F4INX/f4inx-diff-line-demo/pcb/diff-line-2-layers.png

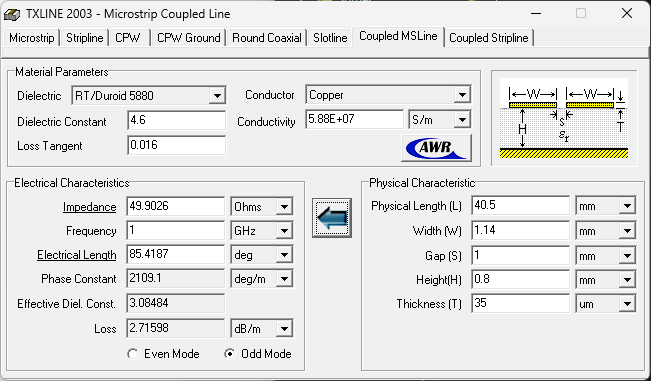
pcb/diff-line-2-layers.png
