F4INX/f4inx-diff-line-demo/pcb/diff-line-4-layers-alt1-even.png

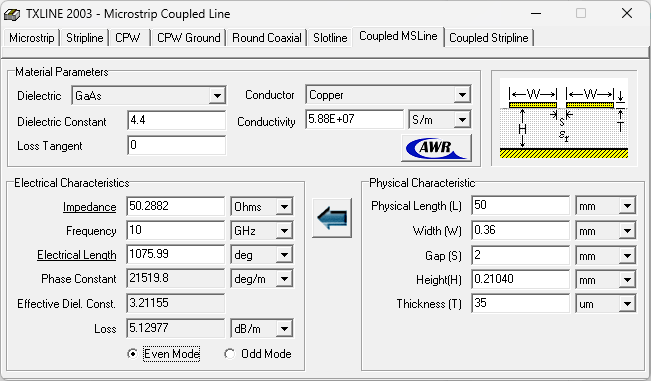
pcb/diff-line-4-layers-alt1-even.png
