F4INX/f4inx-diff-line-demo/pcb/se-line-2-layers.png

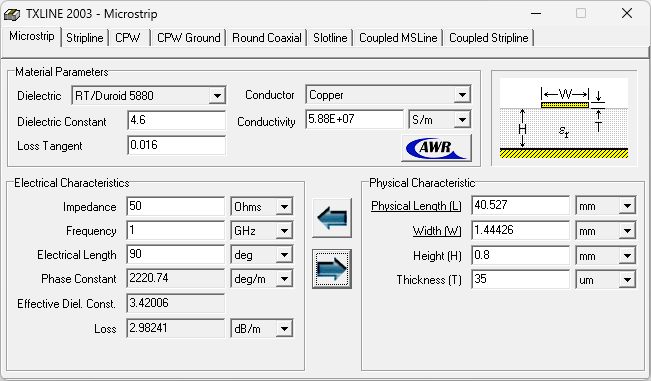
pcb/se-line-2-layers.png
