F4INX/f4inx-diff-line-demo/pictures/20260227_033025.jpg

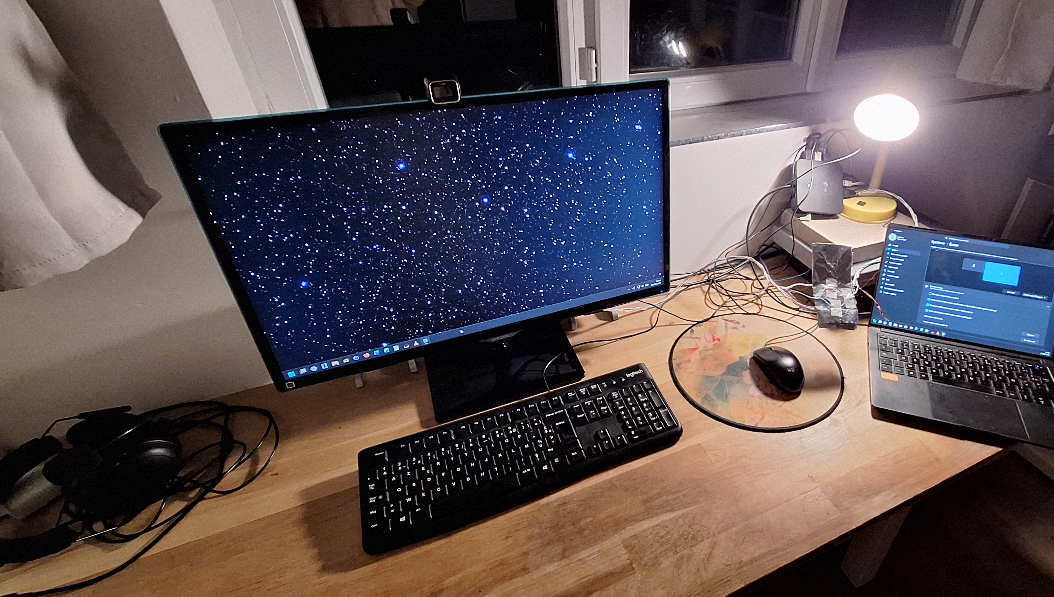
pictures/20260227_033025.jpg
