F4INX/f4inx-diff-line-demo/pictures/20260227_033705.jpg

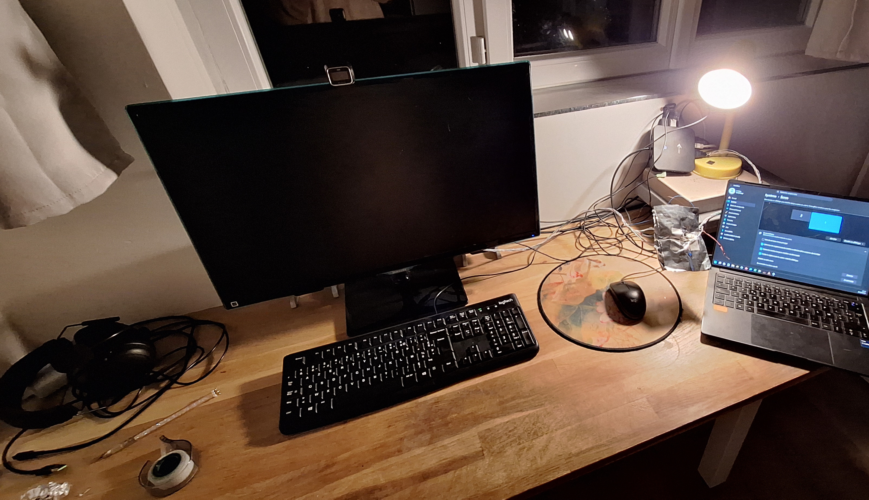
pictures/20260227_033705.jpg
