F4INX/f4inx-diff-line-demo/sim/sim-diff-pair-butterfly-eye.png

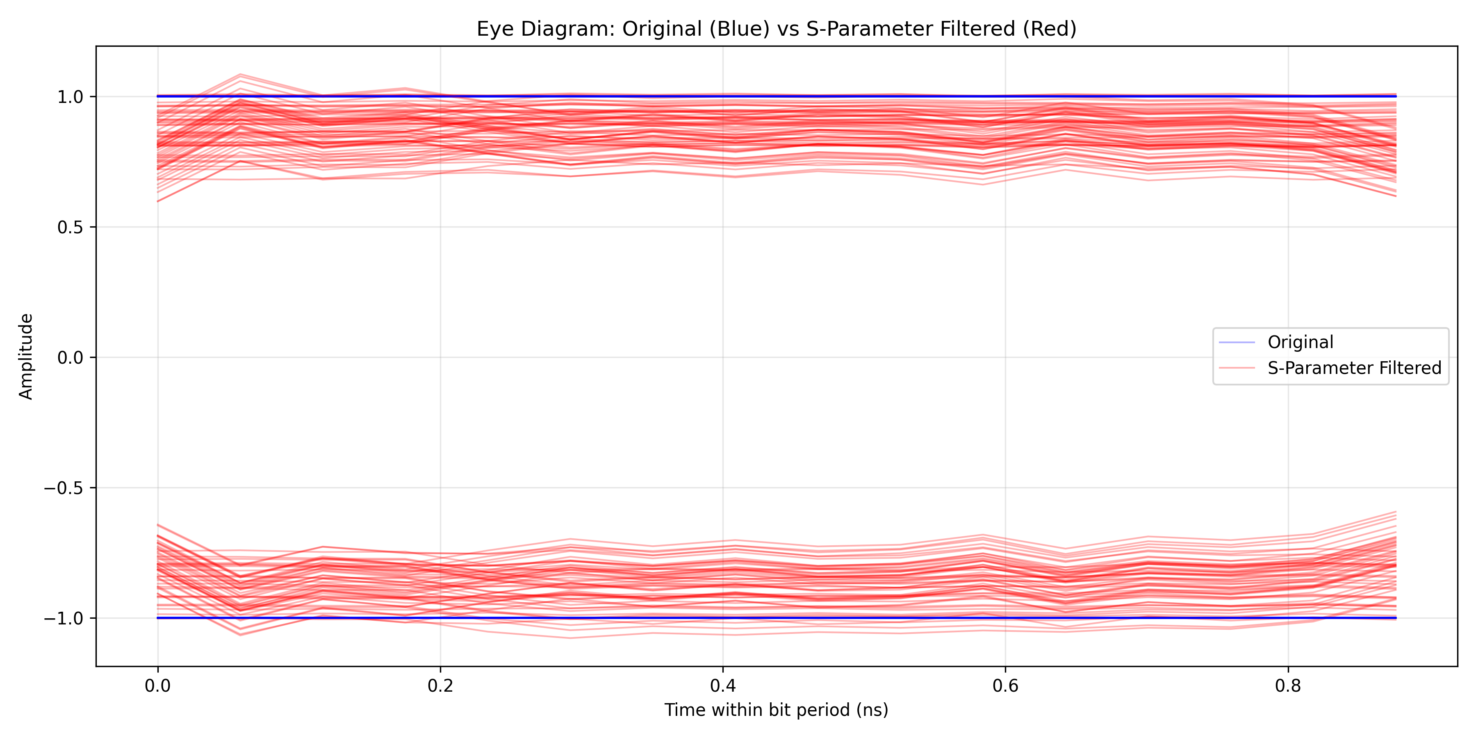
sim/sim-diff-pair-butterfly-eye.png
