F4INX/f4inx-diff-line-demo/sim/sim-diff-pair-cross-butterfly-field.png

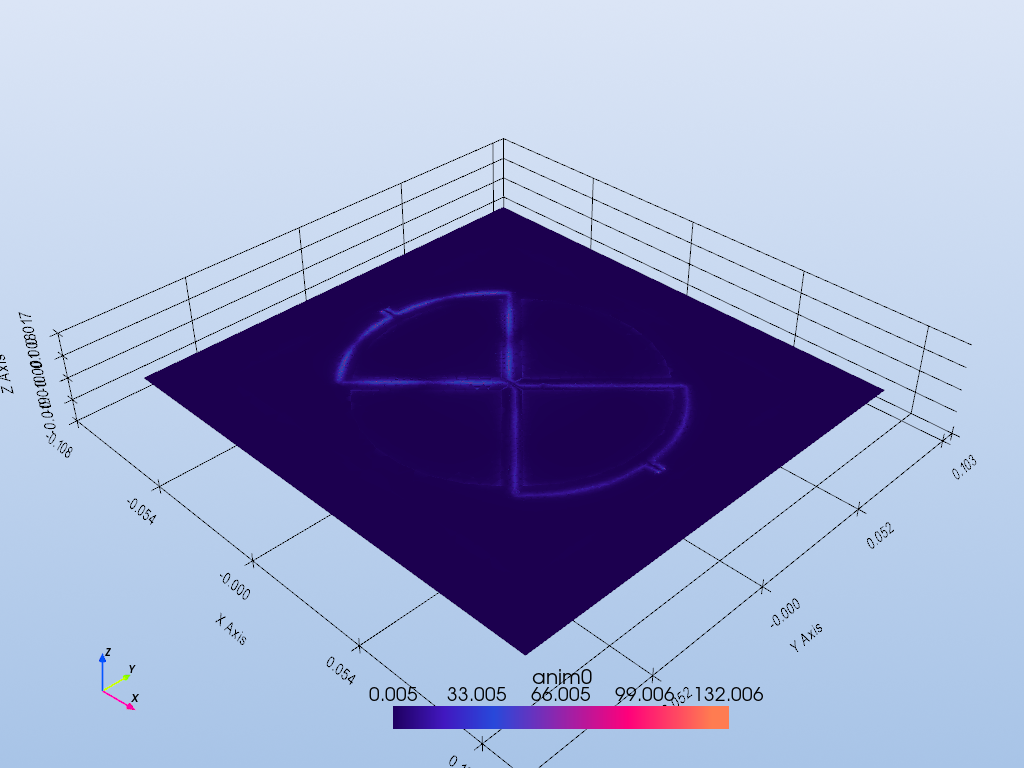
sim/sim-diff-pair-cross-butterfly-field.png
