F4INX/f4inx-diff-line-demo/sim/sim-diff-pair-cross-butterfly-freq.png

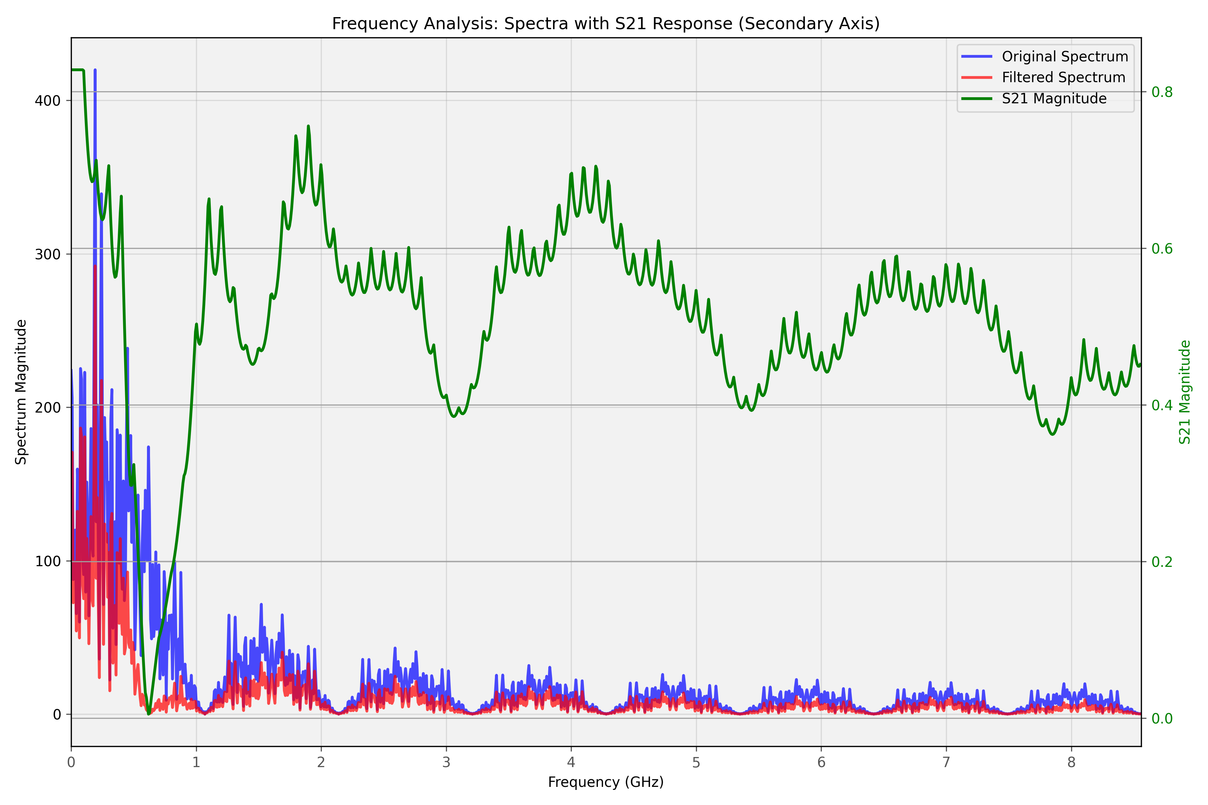
sim/sim-diff-pair-cross-butterfly-freq.png
