F4INX/f4inx-diff-line-demo/sim/sim-diff-pair-cross-butterfly-model-initial.png

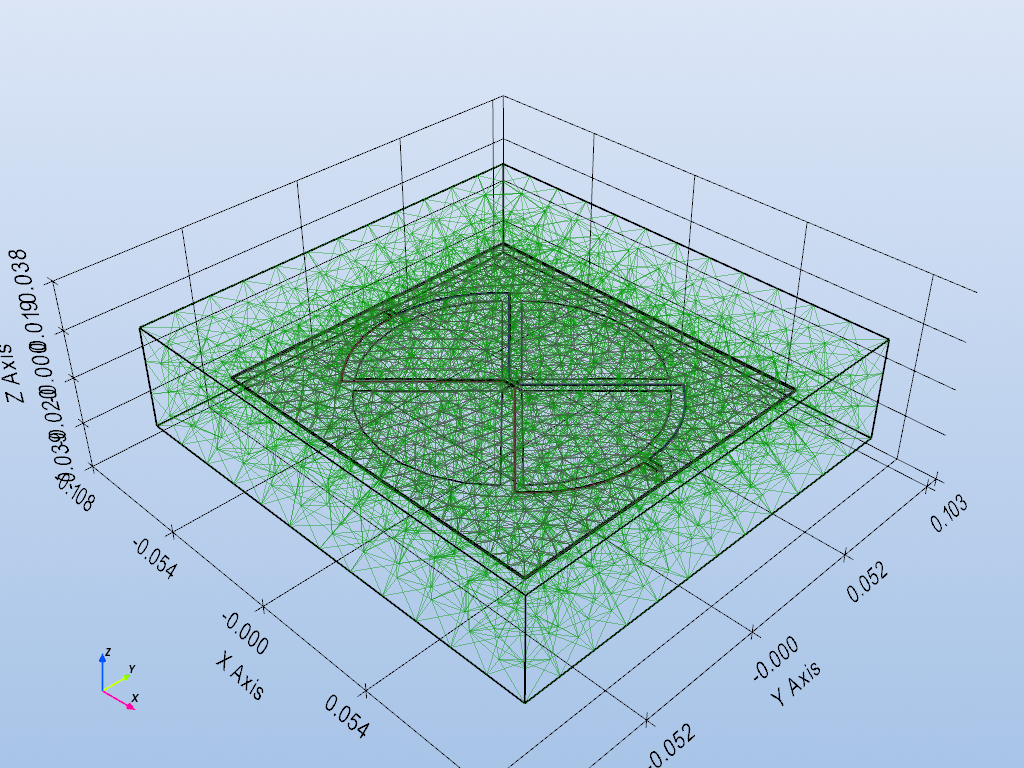
sim/sim-diff-pair-cross-butterfly-model-initial.png
