F4INX/f4inx-diff-line-demo/sim/sim-diff-pair-cross-butterfly-time-domain.png

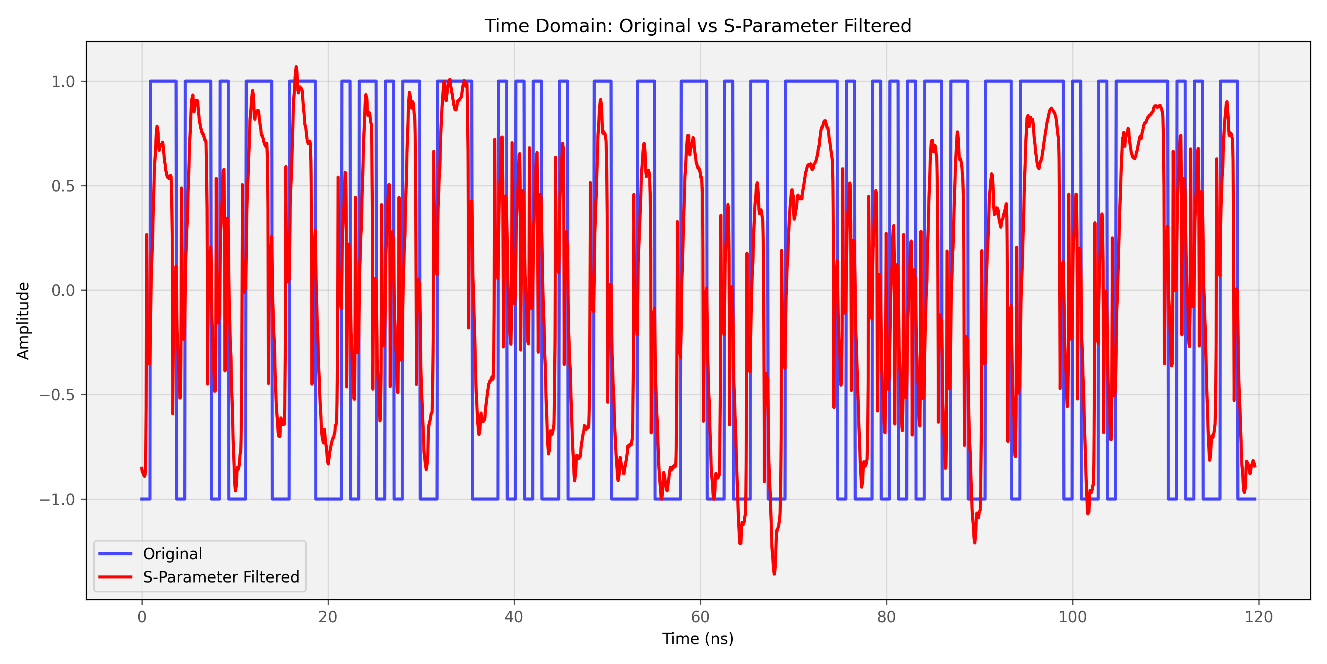
sim/sim-diff-pair-cross-butterfly-time-domain.png
