F4INX/f4inx-diff-line-demo/sim/sim-diff-pair-ref-butterfly-time-domain.png

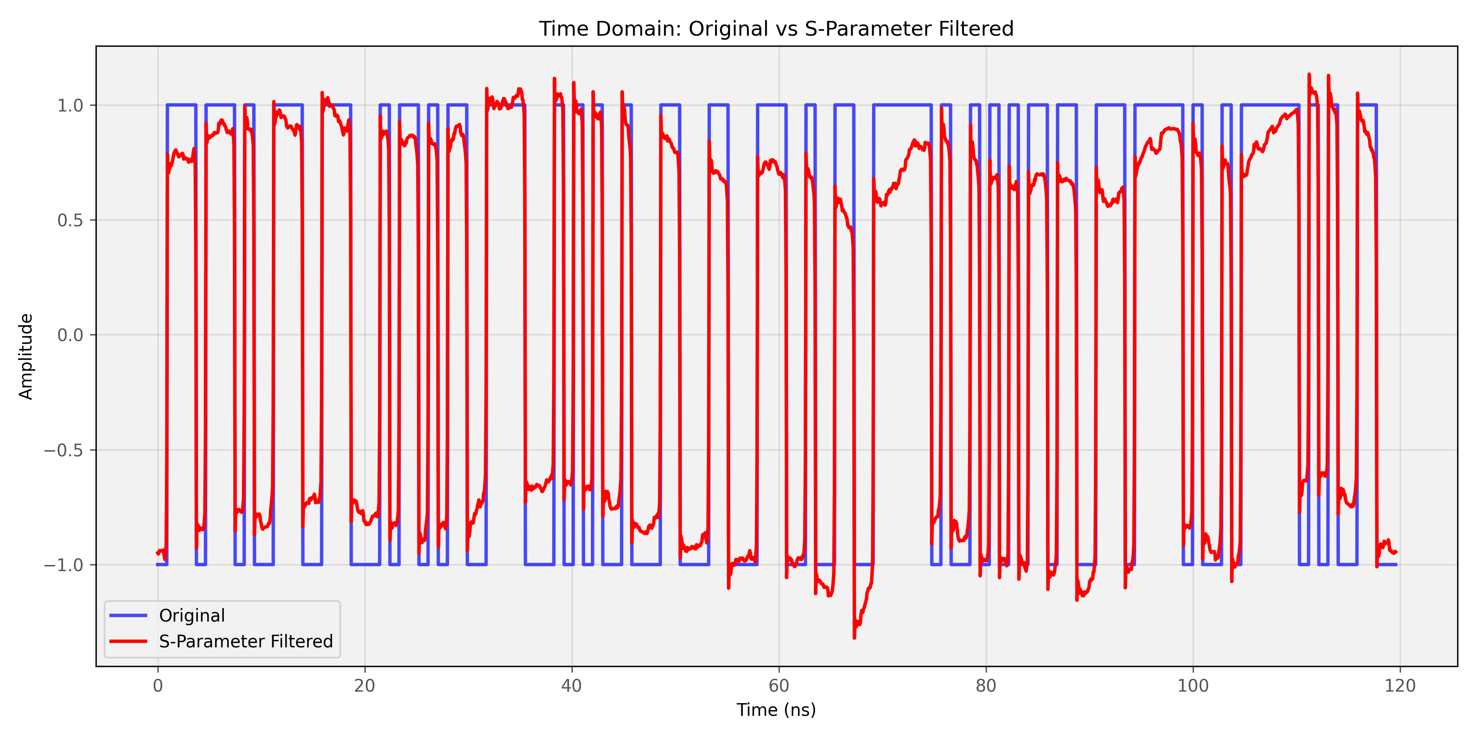
sim/sim-diff-pair-ref-butterfly-time-domain.png
