F4INX/f4inx-diff-line-demo/sim/sim-diff-pair-slot-butterfly-freq.png

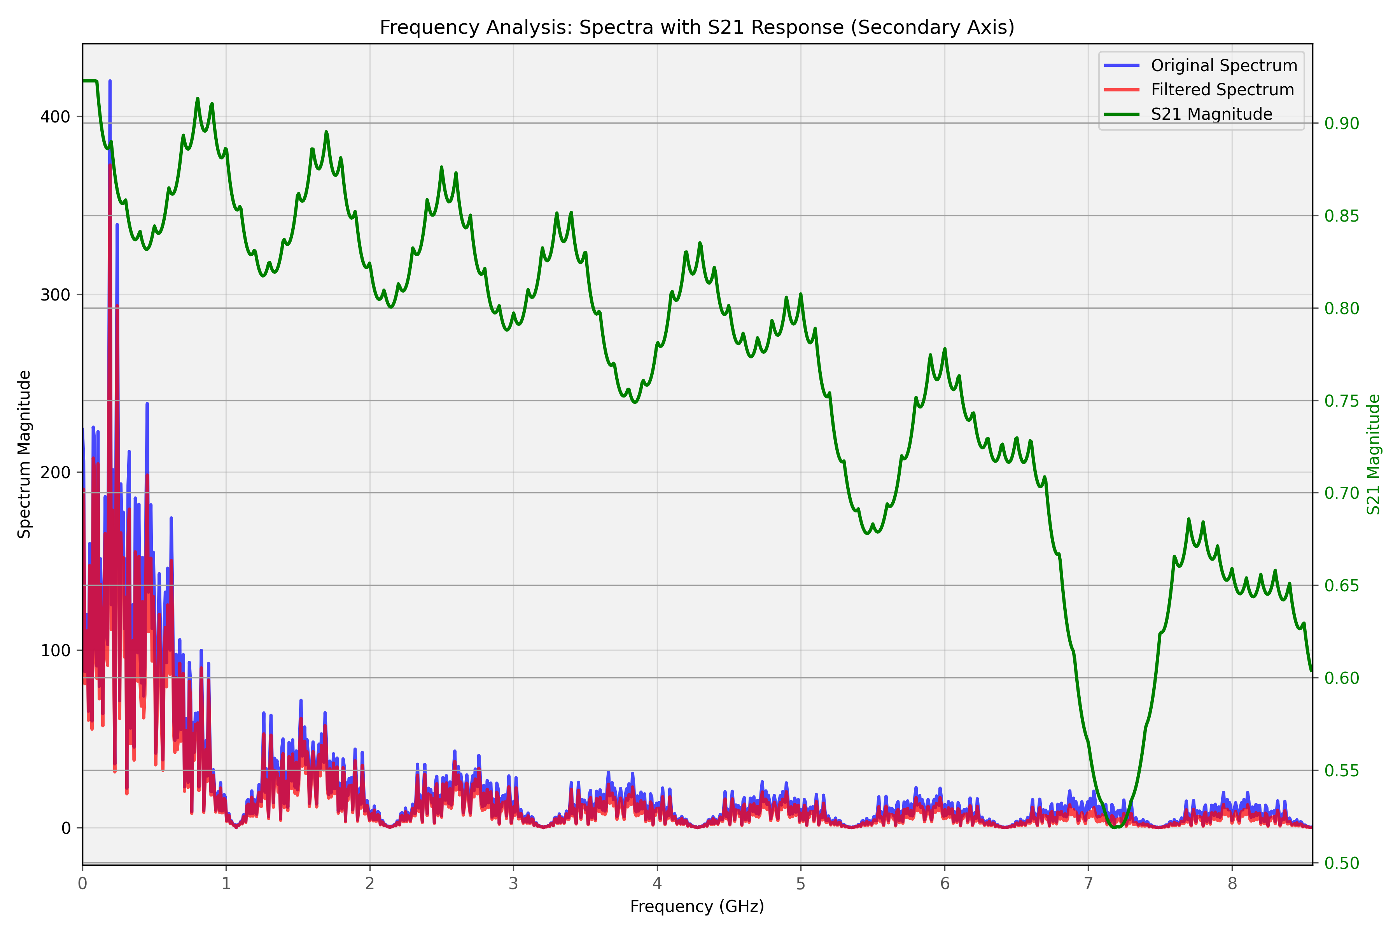
sim/sim-diff-pair-slot-butterfly-freq.png
