F4INX/f4inx-diff-line-demo/sim/sim-diff-pair-slot-butterfly-model-initial.png

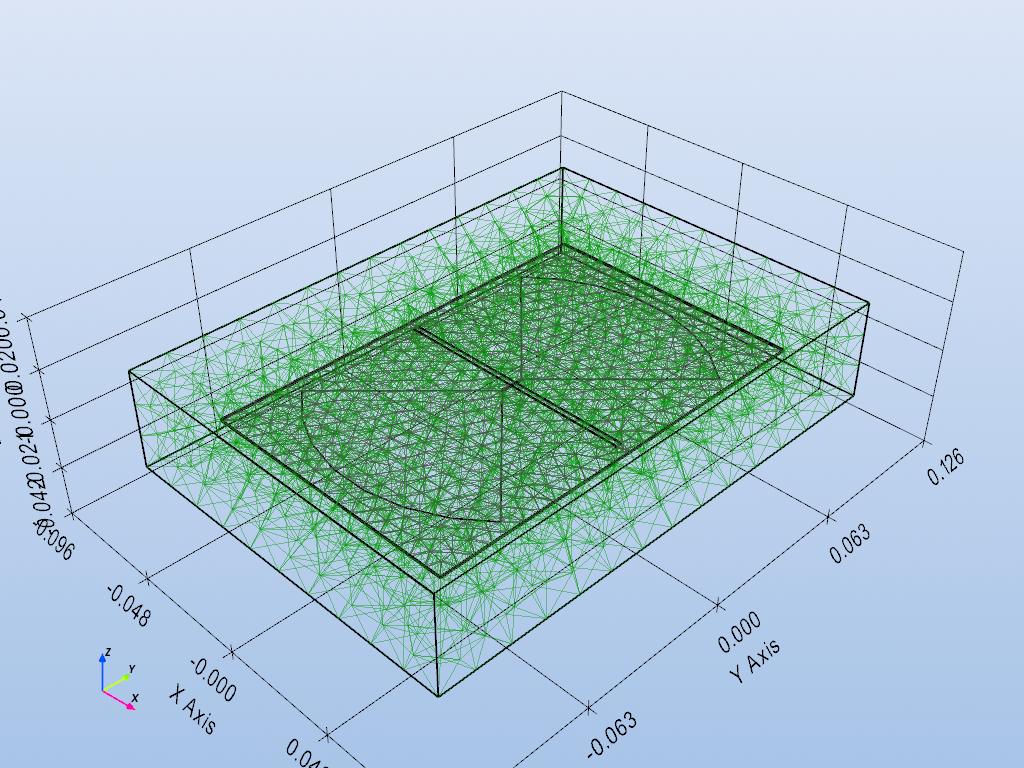
sim/sim-diff-pair-slot-butterfly-model-initial.png
