F4INX/f4inx-diff-line-demo/sim/sim-diff-pair-slot-butterfly-S.png

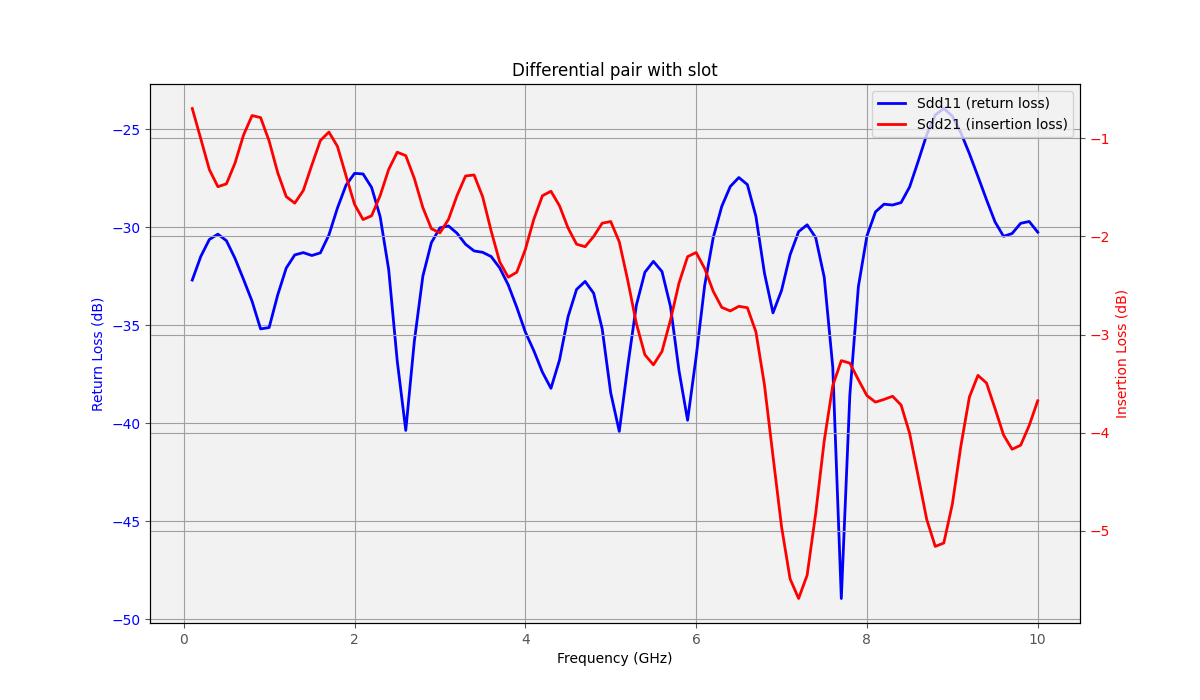
sim/sim-diff-pair-slot-butterfly-S.png
