F4INX/f4inx-diff-line-demo/sim/sim-single-slot-butterfly-freq.png

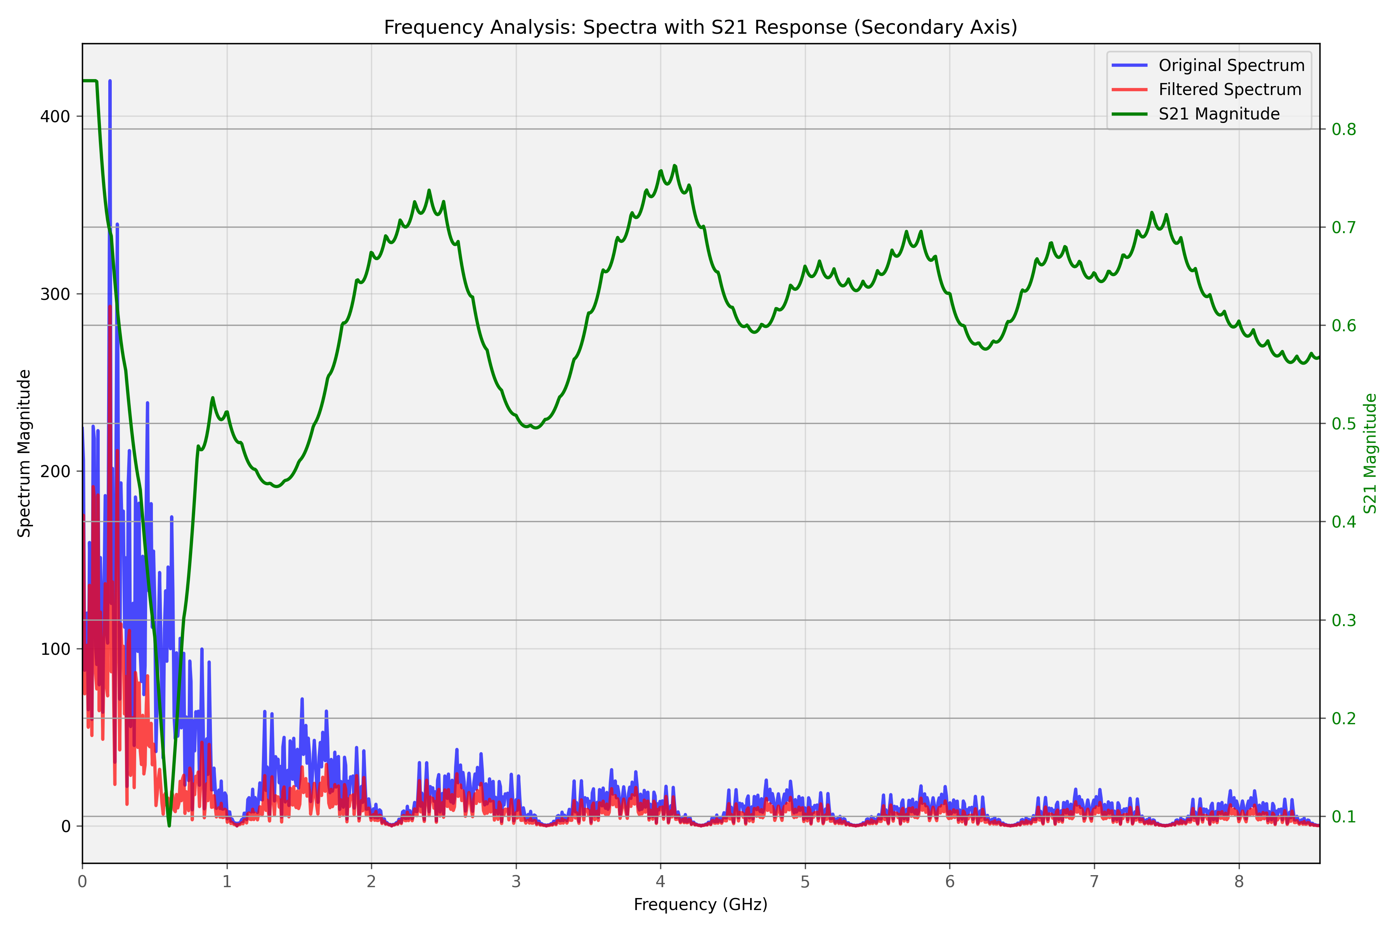
sim/sim-single-slot-butterfly-freq.png
