F4INX/f4inx-diff-line-demo/sim/sim-single-slot-butterfly-model-initial.png

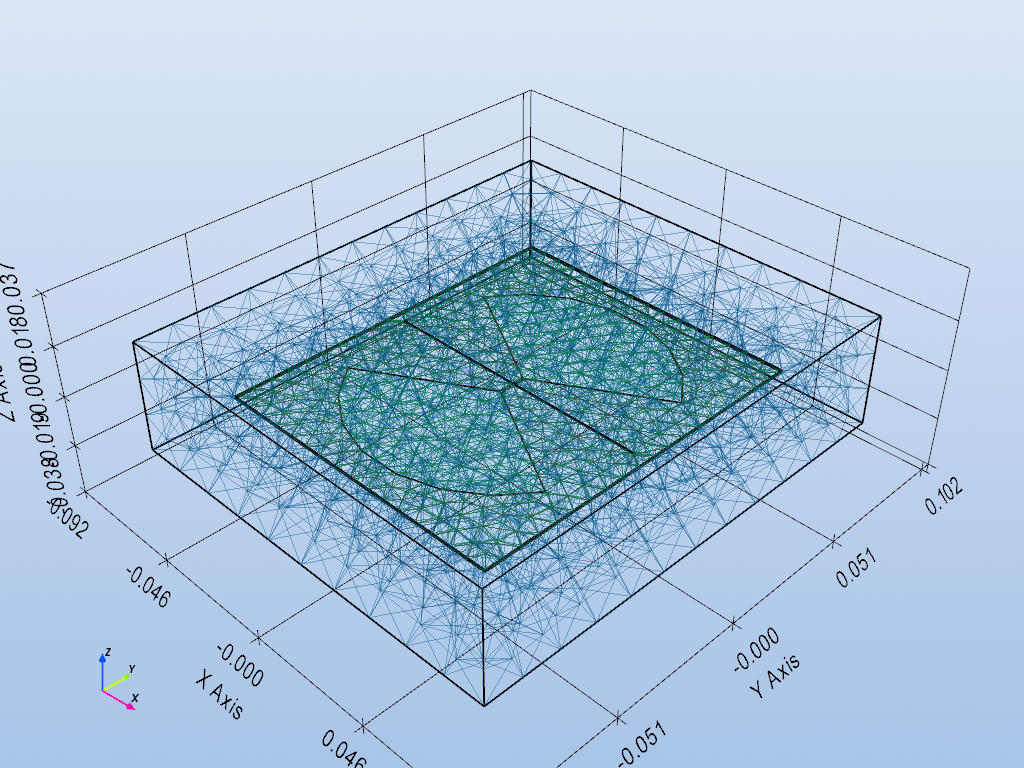
sim/sim-single-slot-butterfly-model-initial.png
