F4INX/f4inx-diff-line-demo/sim/sim-single-slot-butterfly-S.png

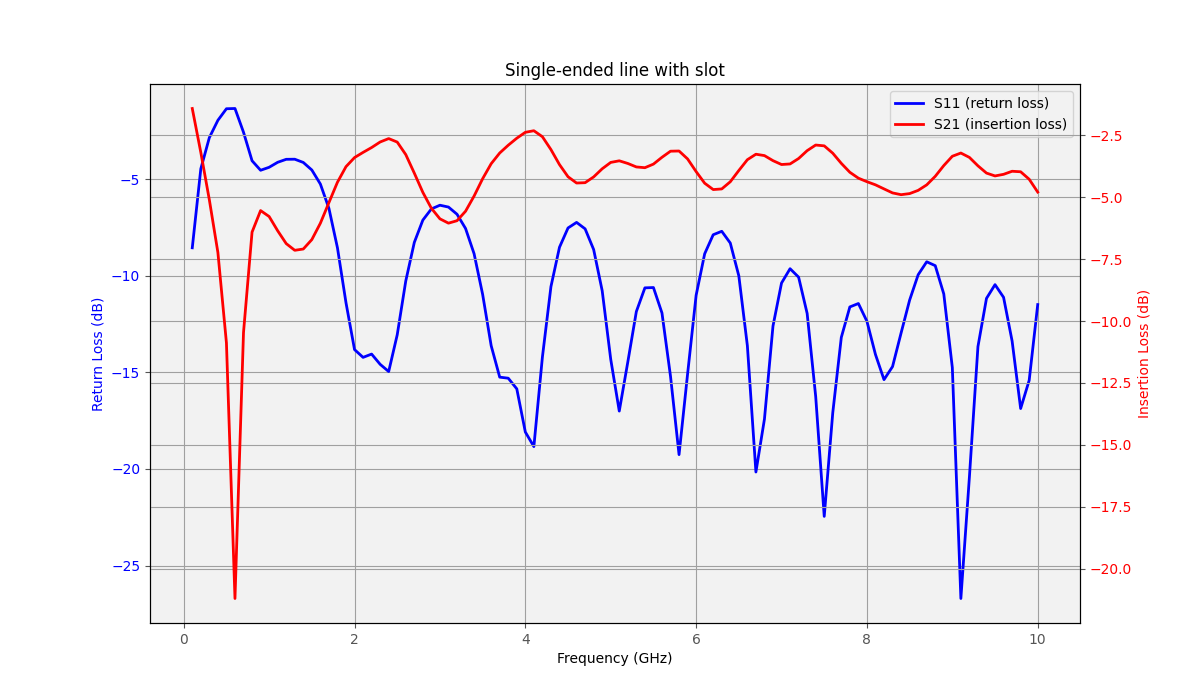
sim/sim-single-slot-butterfly-S.png
