F4INX/f4inx-diff-line-demo/sim/sim-single-slot-butterfly-time-domain.png

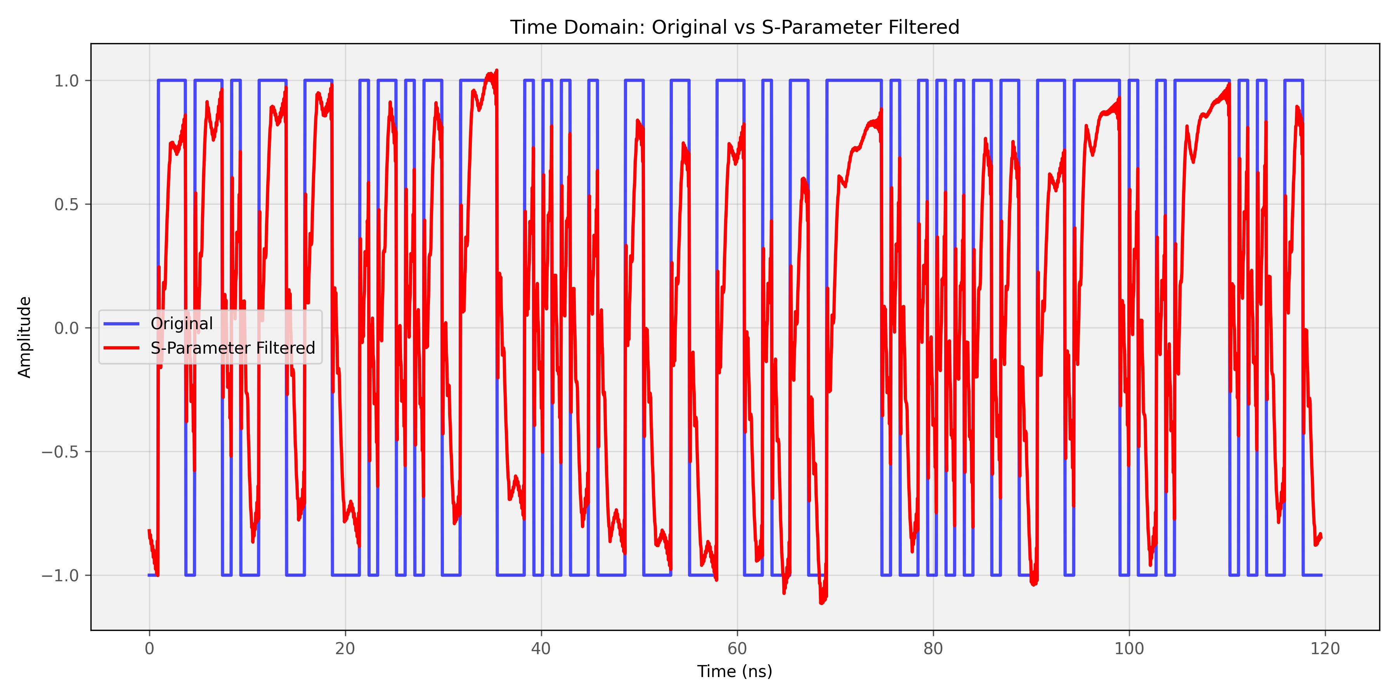
sim/sim-single-slot-butterfly-time-domain.png
